SmartieKarl/custom_clock/include/User_Setup.h

/*                            USER DEFINED SETTINGS
This file is intended to be used by the TFT_eSPI library to define the pin connections for
the ST7789 display on the ESP32 platform. Adjust the pin definitions as necessary to match
your specific hardware setup.
PlatformIO should automatically compile this file before the default library file as long
as it's placed in the 'include' folder.
*/

// User defined information reported by "Read_User_Setup" test & diagnostics example
#define USER_SETUP_INFO "User_Setup"

#define ST7789_DRIVER // Full config option (KEEP THIS)
// #define ST7789_2_DRIVER    // Minimal config option (WILL PROBABLY BREAK SOMETHING)

// #define TFT_RGB_ORDER TFT_RGB  // Colour order Red-Green-Blue
#define TFT_RGB_ORDER TFT_BGR // Colour order Blue-Green-Red

#define TFT_INVERSION_OFF // No inversion

// ST7789 240 x 320 screen
#define TFT_WIDTH 240
#define TFT_HEIGHT 320

#define TFT_MISO -1 //unused
#define TFT_MOSI 23
#define TFT_SCLK 18
#define TFT_CS 15 // Chip select control pin
#define TFT_DC 2  // Data Command control pin
#define TFT_RST 4 // Reset pin
#define TOUCH_CS -1 // Touch screen chip select pin


// Comment out the #defines below with // to stop that font being loaded
// The ESP8366 and ESP32 have plenty of memory so commenting out fonts is not
// normally necessary. If all fonts are loaded the extra FLASH space required is
// about 17Kbytes. To save FLASH space only enable the fonts you need!

#define LOAD_GLCD  // Font 1. Original Adafruit 8 pixel font needs ~1820 bytes in FLASH
#define LOAD_FONT2 // Font 2. Small 16 pixel high font, needs ~3534 bytes in FLASH, 96 characters
#define LOAD_FONT4 // Font 4. Medium 26 pixel high font, needs ~5848 bytes in FLASH, 96 characters
#define LOAD_FONT6 // Font 6. Large 48 pixel font, needs ~2666 bytes in FLASH, only characters 1234567890:-.apm
#define LOAD_FONT7 // Font 7. 7 segment 48 pixel font, needs ~2438 bytes in FLASH, only characters 1234567890:-.
#define LOAD_FONT8 // Font 8. Large 75 pixel font needs ~3256 bytes in FLASH, only characters 1234567890:-.
//#define LOAD_FONT8N // Font 8. Alternative to Font 8 above, slightly narrower, so 3 digits fit a 160 pixel TFT
#define LOAD_GFXFF // FreeFonts. Include access to the 48 Adafruit_GFX free fonts FF1 to FF48 and custom fonts

// Comment out the #define below to stop the SPIFFS filing system and smooth font code being loaded
// this will save ~20kbytes of FLASH
#define SMOOTH_FONT

#define SPI_FREQUENCY 27000000

// Optional reduced SPI frequency for reading TFT
#define SPI_READ_FREQUENCY 20000000

// The XPT2046 requires a lower SPI clock rate of 2.5MHz so we define that here:
#define SPI_TOUCH_FREQUENCY 2500000
